VasilKalchev/LEDDs/enclosure/top_plate/v2.0-bicycle/img/plate-back-1080p.jpg

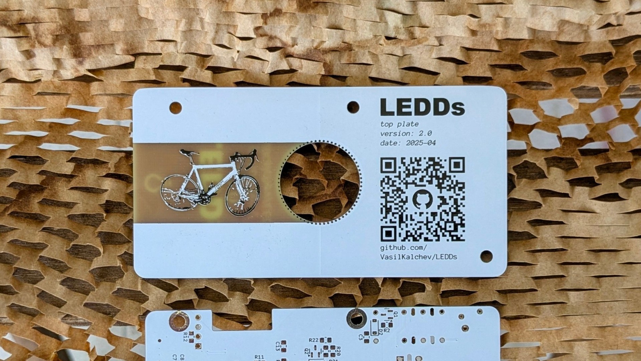
enclosure/top_plate/v2.0-bicycle/img/plate-back-1080p.jpg
