VasilKalchev/LEDDs/hw/export/rotate.webp

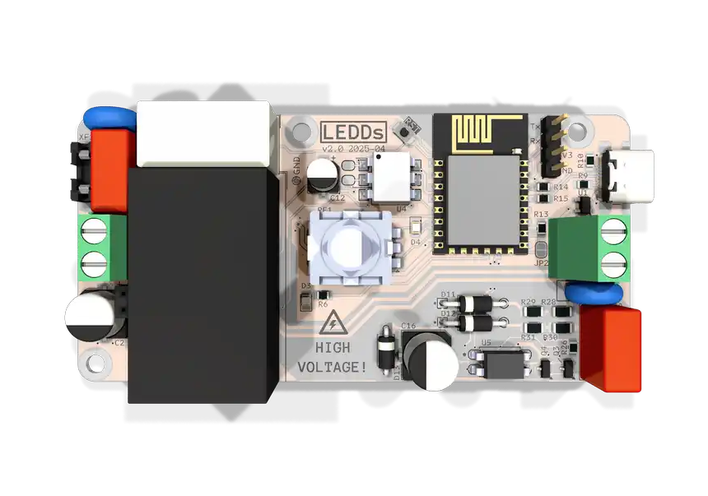
hw/export/rotate.webp
