VasilKalchev/LEDDs/img/ledds-front_1440p.png

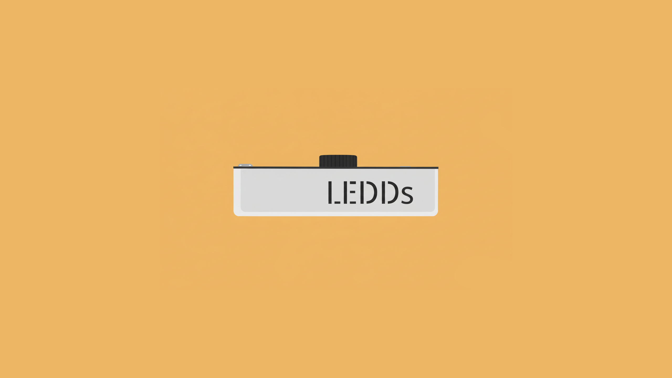
img/ledds-front_1440p.png
