VasilKalchev/LEDDs/img/ledds-front_close_1440p.jpg

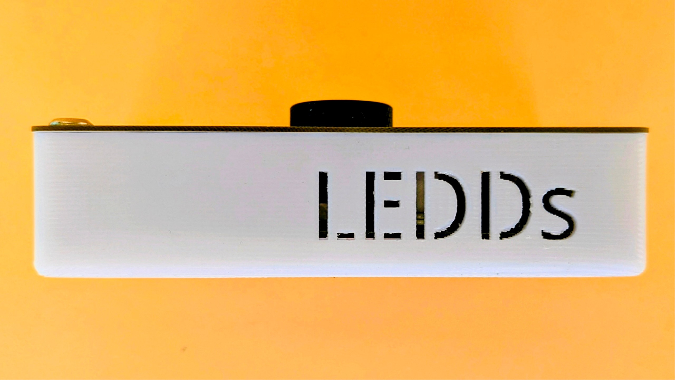
img/ledds-front_close_1440p.jpg
