VasilKalchev/LEDDs/img/ledds_illo-trn_case_bot_orange_1440p.png

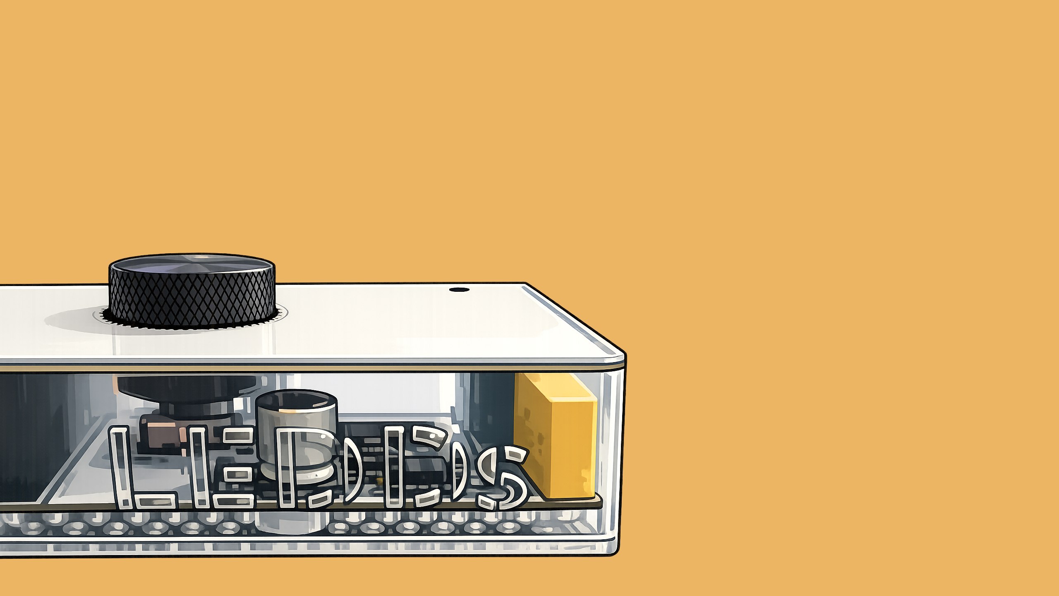
img/ledds_illo-trn_case_bot_orange_1440p.png
