VasilKalchev/LEDDs/img/ledds_on-front_bulb_portrait_1440p.jpg

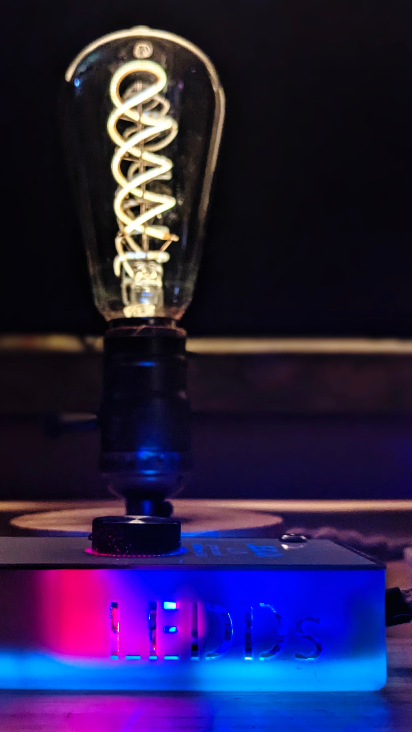
img/ledds_on-front_bulb_portrait_1440p.jpg
