VasilKalchev/LEDDs/img/ledds_on-left_side_1440p.jpg

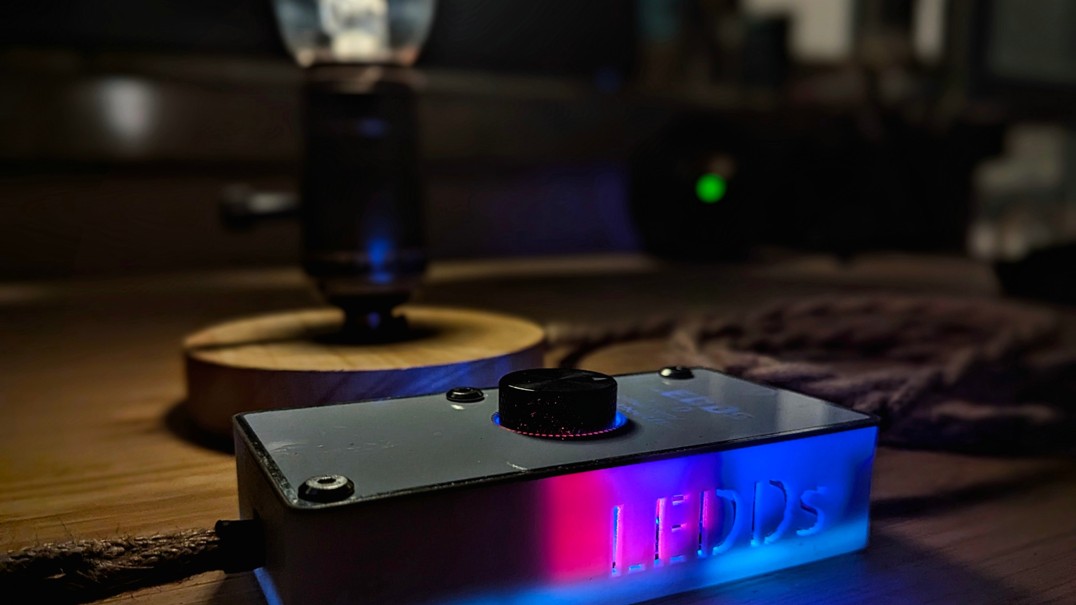
img/ledds_on-left_side_1440p.jpg
