VasilKalchev/LEDDs/img/ledds_on-top_1440p.jpg

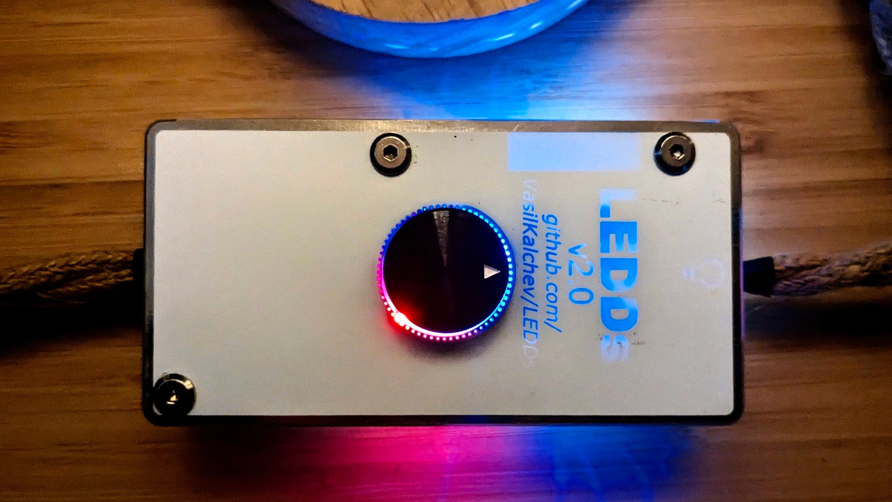
img/ledds_on-top_1440p.jpg
